adityaprasad-sudo/lightsaber/3D_Models/llightsaberfinale-body top left wide.stl

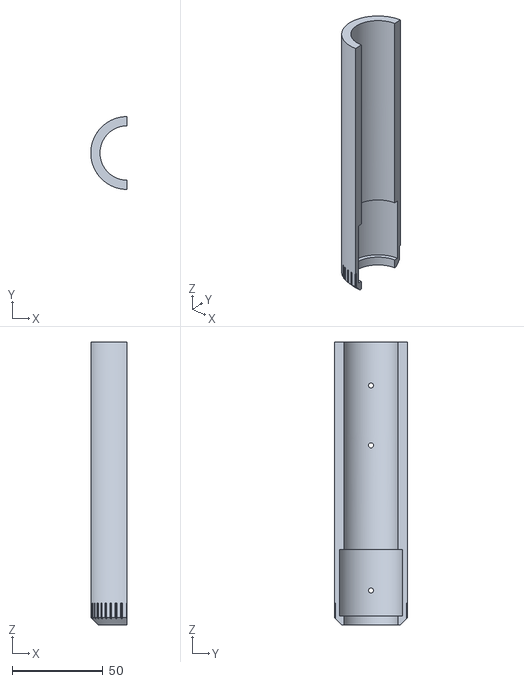
[picture p15: CAD file, 2026-09-30]
3D_Models/llightsaberfinale-body top left wide.stl
20.1 x 40.2 x 156.0
