adityaprasad-sudo/lightsaber/3D_Models/llightsaberfinale-Cut028.stl

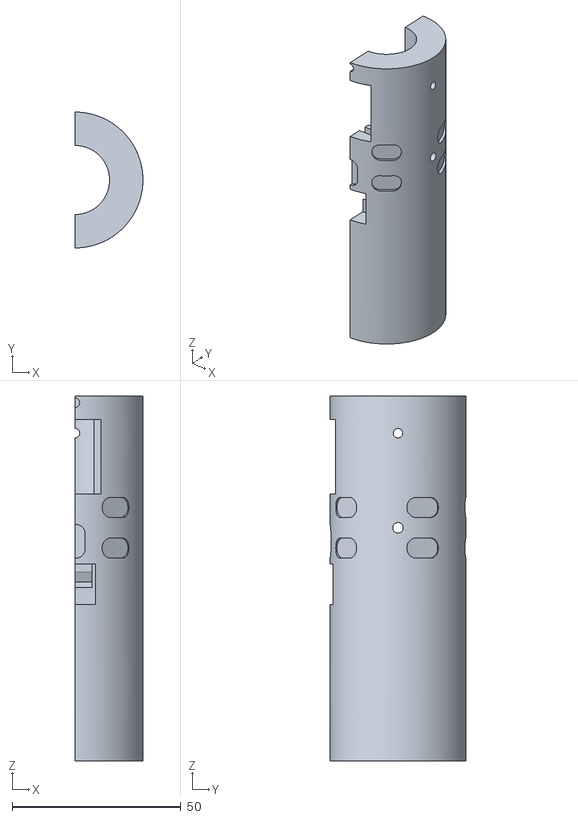
[picture p16: CAD file, 2026-09-30]
3D_Models/llightsaberfinale-Cut028.stl
20.1 x 40.2 x 108.0
