adityaprasad-sudo/lightsaber/3D_Models/llightsaberfinale-Cut027.stl

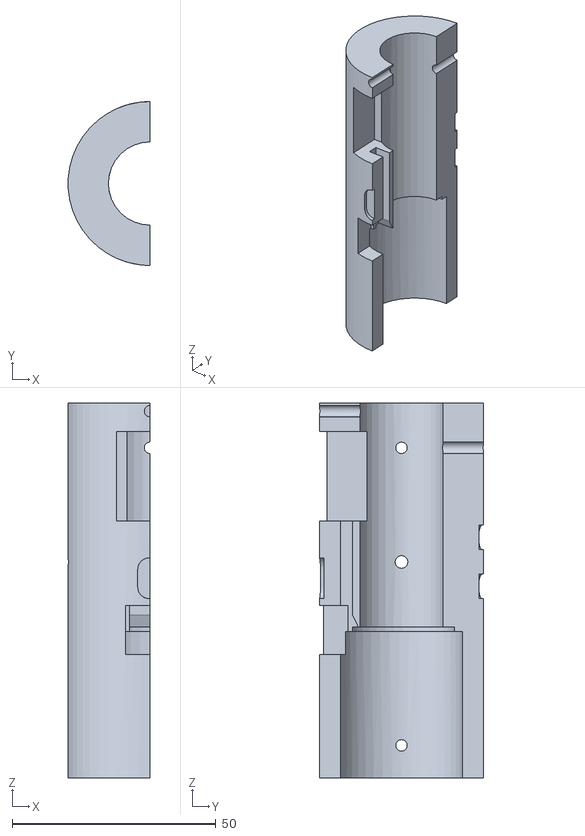
[picture p17: CAD file, 2026-09-30]
3D_Models/llightsaberfinale-Cut027.stl
20.1 x 40.2 x 92.0
