adityaprasad-sudo/lightsaber/3D_Models/llightsaberfinale-screws.stl

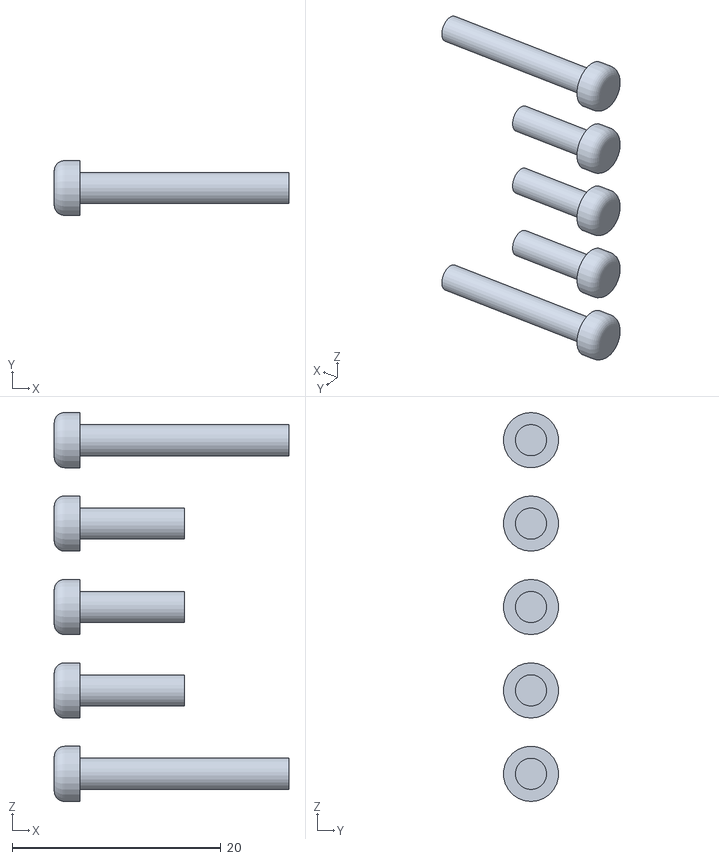
[picture p18: CAD file, 2026-09-30]
3D_Models/llightsaberfinale-screws.stl
22.5 x 5.26 x 37.3
